lucassiglo21/4x40-Bench-LCD-with-USB-C-interface/PCB/pic backpack.png

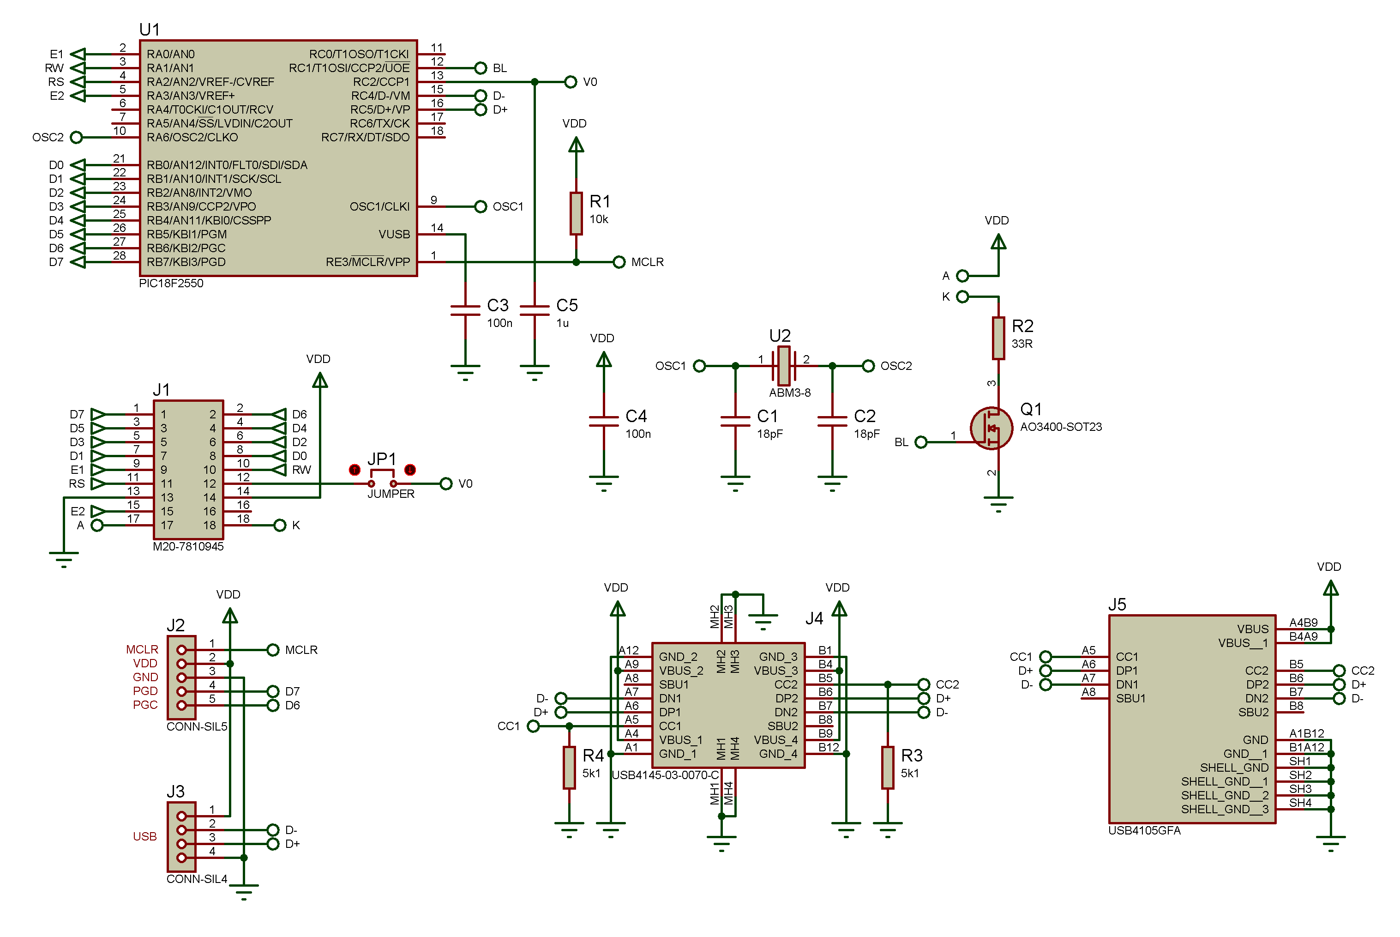
PCB/pic backpack.png
