lucassiglo21/4x40-Bench-LCD-with-USB-C-interface/pictures/20240930_162442.jpg

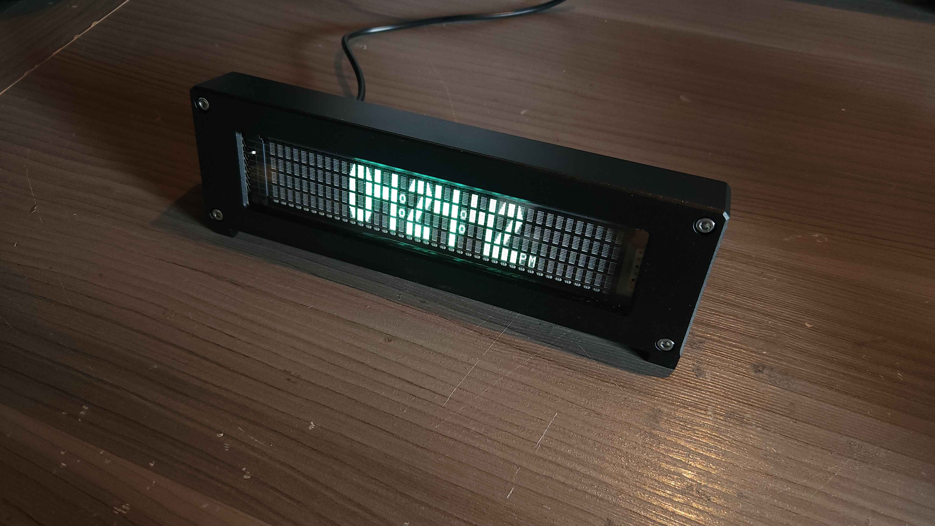
pictures/20240930_162442.jpg
