lucassiglo21/4x40-Bench-LCD-with-USB-C-interface/Case 3d model/ASSEMBLY.sldasm

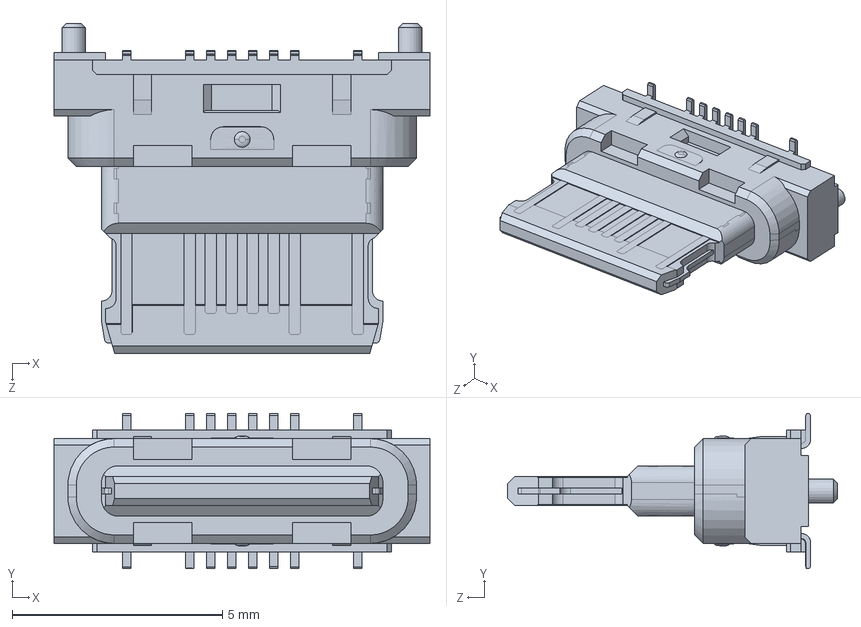
[picture p14: CAD file, 2024-10-03]
Case 3d model/ASSEMBLY.sldasm
8.94 x 3.69 x 7.85 mm
