lucassiglo21/4x40-Bench-LCD-with-USB-C-interface/Case 3d model/Ensamblaje3.SLDASM

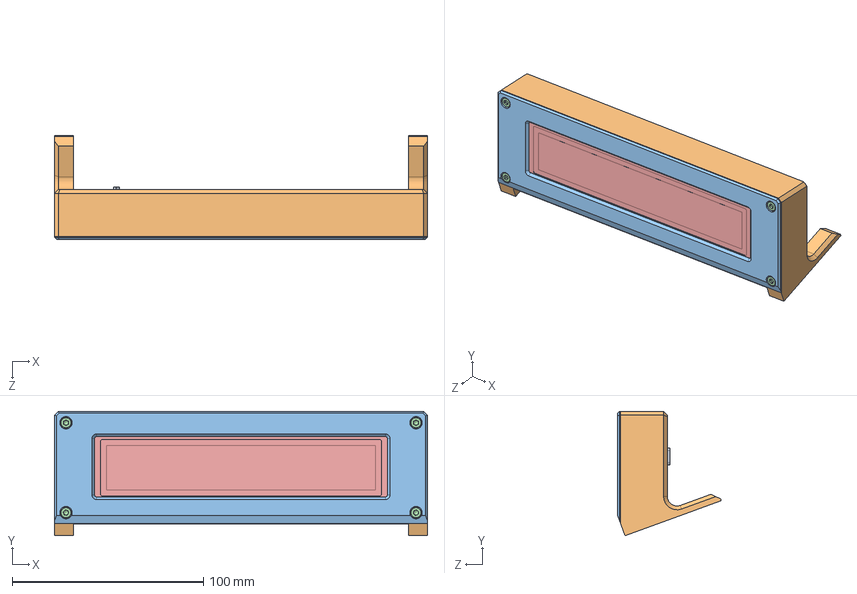
[picture p16: CAD file, 2024-10-03]
Case 3d model/Ensamblaje3.SLDASM
195.0 x 65.1 x 54.2 mm
cu40045-uw1j
Layer_1
=_[0_1_1_2]
Pin_1
Pin_2
Pin_3
Pin_4
Pin_5
Pin_6
Pin_7
Pin_8
Pin_9
Pin_10
Pin_11
Pin_12
Pin_13
Pin_14
Pin_15
Pin_16
Pin_17
Pin_18
Pin_19
Pin_20
Pin_21
Pin_22
Pin_23
Pin_24
Pin_25
Pin_26
Pin_27
Pin_28
=_[0_1_1_3]
=_[0_1_1_4]
=_[0_1_1_5]
Pin_1_2 x 5
Pin_2_2 x 5
Pin_1_3
Pin_2_3
=_[0_1_1_2]_2
=_[0_1_1_4]_2
Pin_1_4 x 4
Pin_2_4 x 4
Imported
Pieza6
Pieza7
socket head cap screw_iso x 4
