lucassiglo21/4x40-Bench-LCD-with-USB-C-interface/Case 3d model/to manufacture/vfdfront.STEP

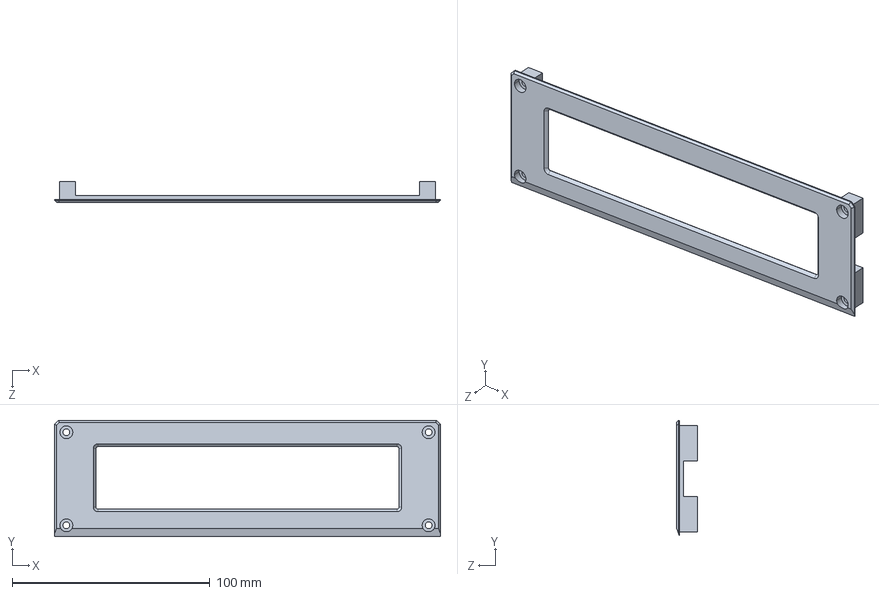
[picture p17: CAD file, 2024-10-03]
Case 3d model/to manufacture/vfdfront.STEP
195.0 x 58.7 x 10.5 mm
