lucassiglo21/4x40-Bench-LCD-with-USB-C-interface/Case 3d model/to manufacture/vfdback.STEP

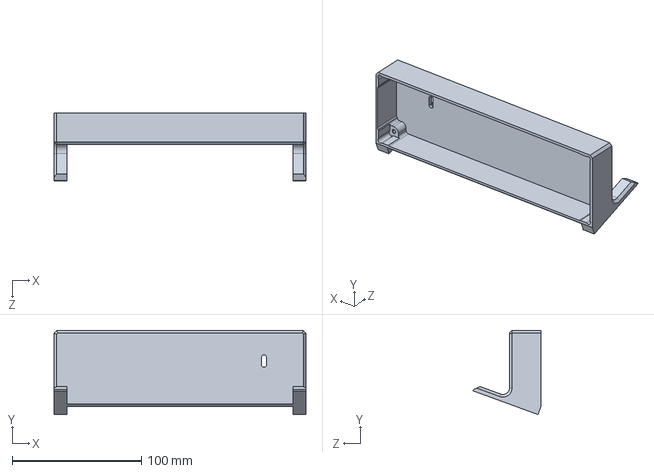
[picture p18: CAD file, 2024-10-03]
Case 3d model/to manufacture/vfdback.STEP
195.0 x 65.1 x 52.7 mm
